simonmacias/Visiere-Laser/VISI70/Images/1.JPG

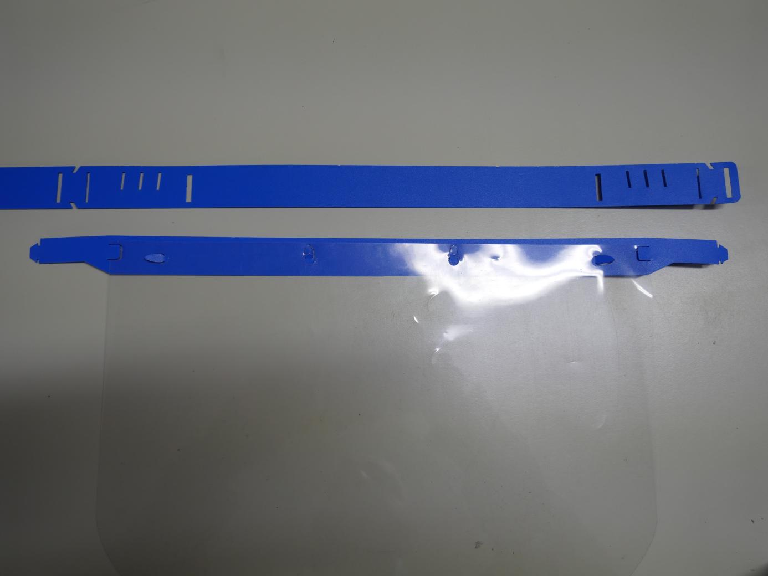
VISI70/Images/1.JPG
