simonmacias/Visiere-Laser/VISI70/Images/3.JPG

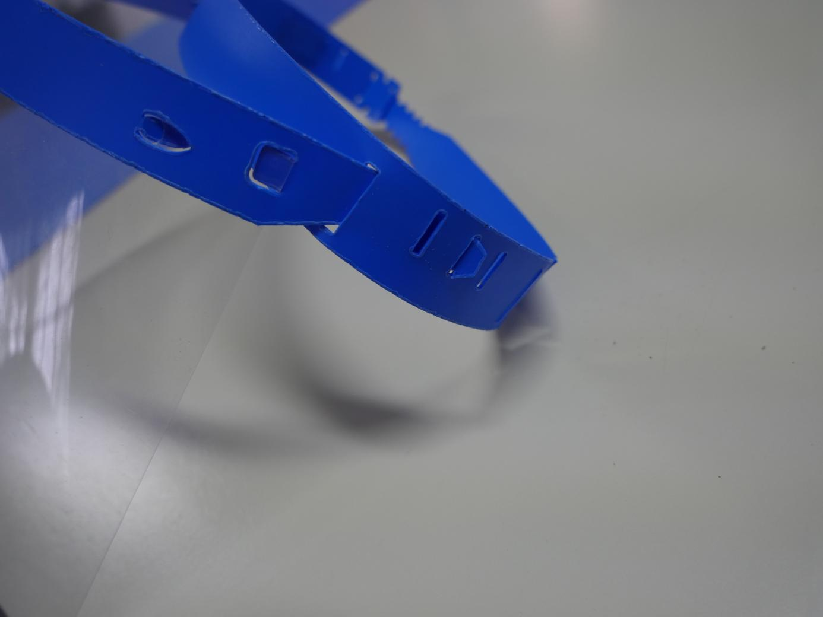
VISI70/Images/3.JPG
