simonmacias/Visiere-Laser/VISI70/Images/5.JPG

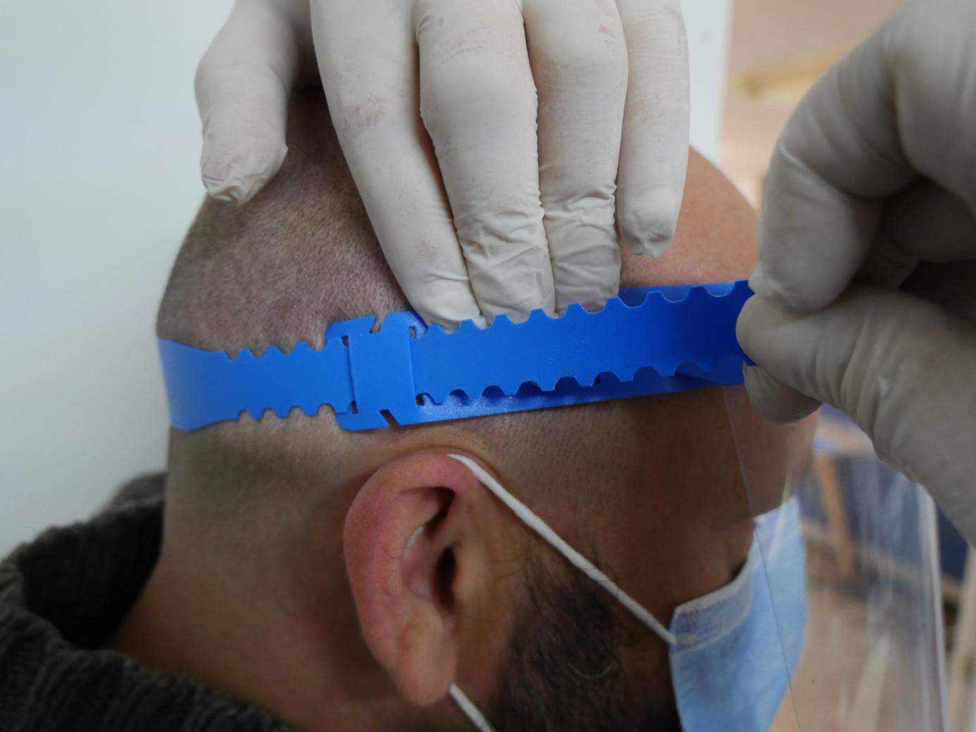
VISI70/Images/5.JPG
